Liaoliaoliaole/BMS/blockdiagram/block diagram.png

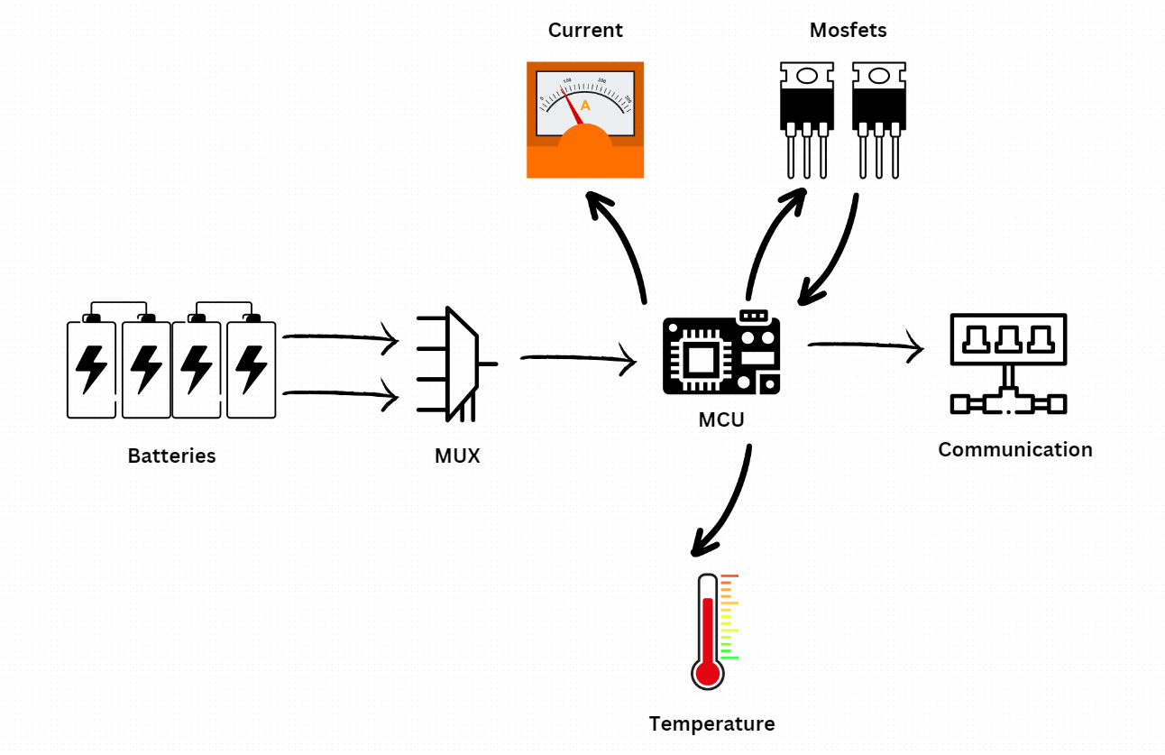
blockdiagram/block diagram.png
