Liaoliaoliaole/BMS/blockdiagram/block_diagram.jpg

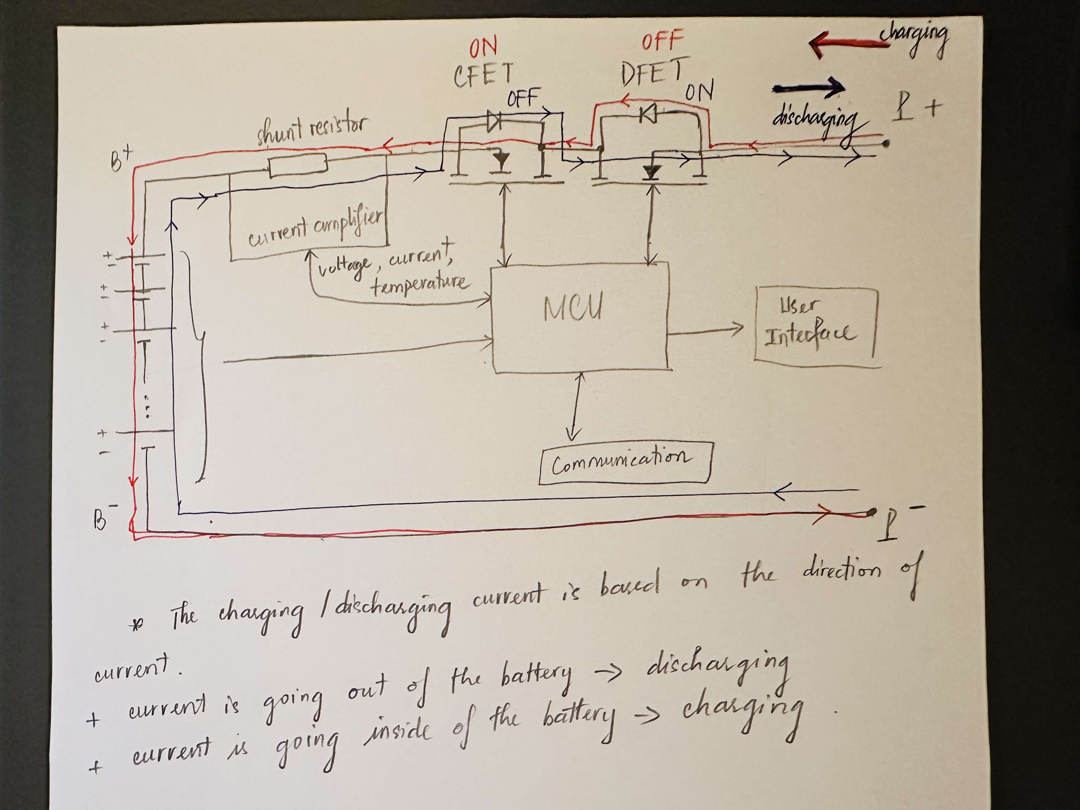
blockdiagram/block_diagram.jpg
