Liaoliaoliaole/BMS/prototyping/Lab2_temperature_measurement/Capture_lm35_test.PNG

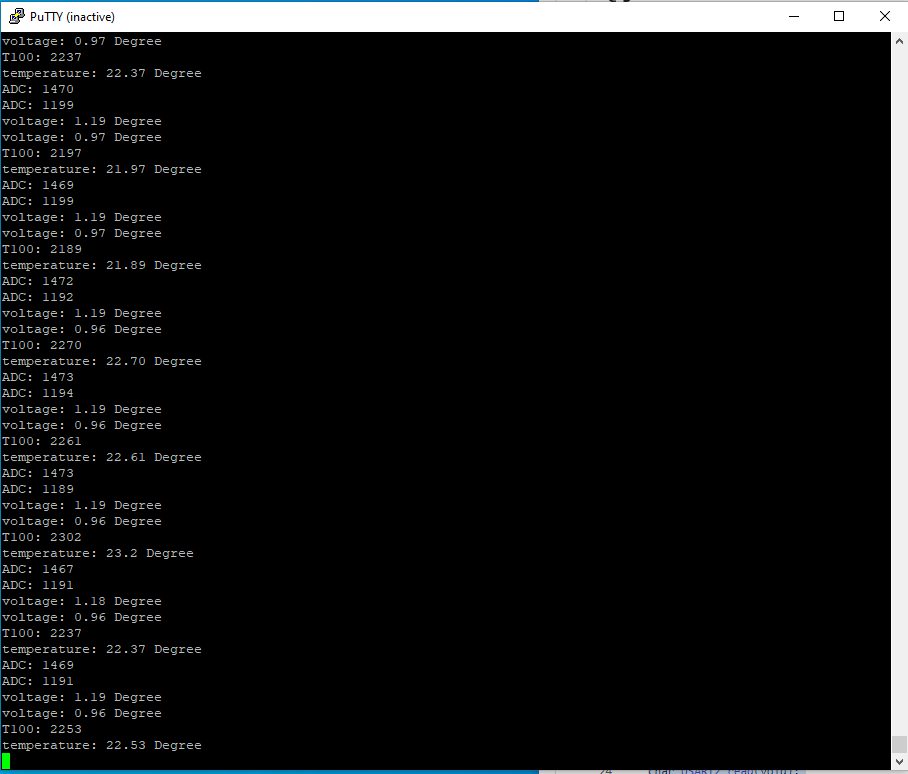
prototyping/Lab2_temperature_measurement/Capture_lm35_test.PNG
