Liaoliaoliaole/BMS/simulation/current_protection_simulation/current_protection.asc

D1: diode; 1N4148
D2: diode; 1N4148
I1: current; 9.4
R1: res; 0.01
R2: res; 910
R3: res; 910
R4: res; 32k
R5: res; 32k
R6: res; 10k
U1: UniversalOpAmp
U2: UniversalOpAmp
V1: voltage; 12
V2: voltage; 2.9
Named nets: 0, +12V, Vout_2, +2.9V, Vout_1
.dc I1 -9.4 10 0.01
.lib nat_semi.lib
.lib nat_semi.lib
