Liaoliaoliaole/BMS/simulation/short circuit protection_simulation/short_circuit_protection.asc

M1: nmos; IRFR2607Z
R1: res; 10
R2: res; 1k
U1: PC817A
V1: voltage; 12
V2: voltage; 12V
V3: voltage; PULSE(0 2 5m 10n 10n 10m 20m 1)
Named nets: 0, V2, D, vcc, V3
.tran 0 20m 0 100u
