Liaoliaoliaole/BMS/prototyping/Lab2_temperature_measurement/test_lm35.c

/* Includes */
#include <stddef.h>
#include "stm32l1xx.h"
#include "nucleo152start.h"
#include <stdio.h>
#include <stdlib.h>


int read_adc(uint8_t channel)
{
	int result=0;
	// Set the ADC channel
	ADC1->SQR5 = channel;      // Conversion sequence starts at selected channel
	ADC1->CR2 |= 1;            // Bit 0, ADC on/off (1=on, 0=off)
	ADC1->CR2 |= 0x40000000;   // Start conversion
	while (!(ADC1->SR & 2)){}  // Wait for conversion complete
	result = ADC1->DR;     // Read conversion result

	ADC1->CR2 &= ~1;           // Bit 0, ADC on/off (1=on, 0=off)
	return result;
}


void USART2_write(char data)
{
	//wait while TX buffer is empty
	while(!(USART2->SR&0x0080)){} 	//TXE: Transmit data register empty. p736-737
		USART2->DR=(data);		//p739
}

char USART2_read()
{
	char data=0;
	//wait while RX buffer data is ready to be read
	while(!(USART2->SR&0x0020)){} //Bit 5 RXNE: Read data register not empty
		data=USART2->DR;			//p739
		return data;
}

void delay_Ms(int delay)
{
	int i=0;
	for(; delay>0;delay--)
		for(i=0;i<2460;i++); //measured with oscilloscope
}

void print_temperature100(int t)
{
	char buf[100];
	sprintf(buf, "T100: %d", t);

	int len=0;
	while(buf[len]!='\0')
	  	len++;

	for(int i=0;i<len;i++)
	{
	  	USART2_write(buf[i]);
	}

	 USART2_write('\n');
	 USART2_write('\r');
}

void print_temperature(int temp)
{
	char buf[100];
	int temp_degree=0;
	int temp_decimals=0;

	temp_degree=(int)temp/100;
	temp_decimals= abs((int)temp%100);
  	sprintf(buf,"temperature: %d.%d Degree",temp_degree,temp_decimals);

  	int len=0;
  	while(buf[len]!='\0')
  		len++;

  	for(int i=0;i<len;i++)
  	{
  		USART2_write(buf[i]);
  	}

  	USART2_write('\n');
  	USART2_write('\r');
}

void print_adc(int adc_read)
{
	char buf[100];
	sprintf(buf, "ADC: %d", adc_read);

	int len=0;
	while(buf[len]!='\0')
	  	len++;

	for(int i=0;i<len;i++)
	{
	  	USART2_write(buf[i]);
	}

	 USART2_write('\n');
	 USART2_write('\r');
}

void print_volt(float volt)
{
	float volt100= volt*100;
	char buf[100];
	int temp_degree=0;
	int temp_decimals=0;

	temp_degree=(int)volt100/100;
	temp_decimals= abs((int)volt100%100);
  	sprintf(buf,"voltage: %d.%d Degree",temp_degree,temp_decimals);

  	int len=0;
  	while(buf[len]!='\0')
  		len++;

  	for(int i=0;i<len;i++)
  	{
  		USART2_write(buf[i]);
  	}

  	USART2_write('\n');
  	USART2_write('\r');
}



float get_voltage(int adc){
	float voltage = (float)adc*(3.32/4095.0);
	return voltage;
}

int get_temp(float volt){
	int temp = volt*100*100;//temp *100, without fraction
	return temp;
}

void USART2_Init(void)
{

	RCC->APB1ENR|=0x00020000; 	//set bit 17 (USART2 EN)
	RCC->AHBENR|=0x00000001; 	//enable GPIOA port clock bit 0 (GPIOA EN)
	GPIOA->AFR[0]=0x00000700;	//GPIOx_AFRL p.188,AF7 p.177
	GPIOA->AFR[0]|=0x00007000;	//GPIOx_AFRL p.188,AF7 p.177
	GPIOA->MODER|=0x00000020; 	//MODER2=PA2(TX) to mode 10=alternate function mode. p184
	GPIOA->MODER|=0x00000080; 	//MODER2=PA3(RX) to mode 10=alternate function mode. p184

	USART2->BRR = 0x00000D05;	//9600BAUD and crystal 32MHz. p710, 116
	USART2->CR1 = 0x00000008;	//TE bit. p739-740. Enable transmit
	USART2->CR1 |= 0x00000004;	//RE bit. p739-740. Enable receiver
	USART2->CR1 |= 0x00002000;	//UE bit. p739-740. Uart enable
}


int main(void)
{
  /* Configure the system clock to 32 MHz and update SystemCoreClock */
  SetSysClock();
  SystemCoreClockUpdate();
  USART2_Init();


  //set up pin PA5 for LED
  RCC->AHBENR |= 1;				//enable GPIOA clock
  GPIOA->MODER&=~0x00000C00;	//clear pin mode
  GPIOA->MODER|=0x00000400;		//set pin PA5 to output model

  //set up pin PA0 and PA1 for analog input
  GPIOA->MODER|=0x3;			//PA0 analog (A0)
  GPIOA->MODER|=0xC;			//PA1 analog (A1)

  //setup ADC1. p272
  RCC->APB2ENR|=0x00000200;		//enable ADC1 clock
  ADC1->CR2=0;					//bit 1=0: Single conversion mode
  ADC1->SMPR3=7;				//384 cycles sampling time for channel 0 (longest)
  ADC1->CR1&=~0x03000000;		//resolution 12-bit

  /* Infinite loop */
  while (1)
  {
	  int result_arr0=0;
	  int result_arr1=0;
	  int diff_adc=0;
	  float v0=0;
	  float v1=0;
	  int temp=0;

	result_arr0 = read_adc(0);
	delay_Ms(50);

	result_arr1 = read_adc(1);
	delay_Ms(50);

	print_adc(result_arr0);
	print_adc(result_arr1);

	v0=get_voltage(result_arr0);
	v1=get_voltage(result_arr1);

	print_volt(v0);
	print_volt(v1);

	float v=v0-v1;
	temp=get_temp(v);
	print_temperature100(temp);


	delay_Ms(1000);
	print_temperature(temp);
	delay_Ms(1000);
  }
  return 0;
}
